dededecline/SST60/KiCad Project Files/MCU.kicad_sch

## KiCad design KiCad Project Files/MCU.kicad_sch (2022-08-14)

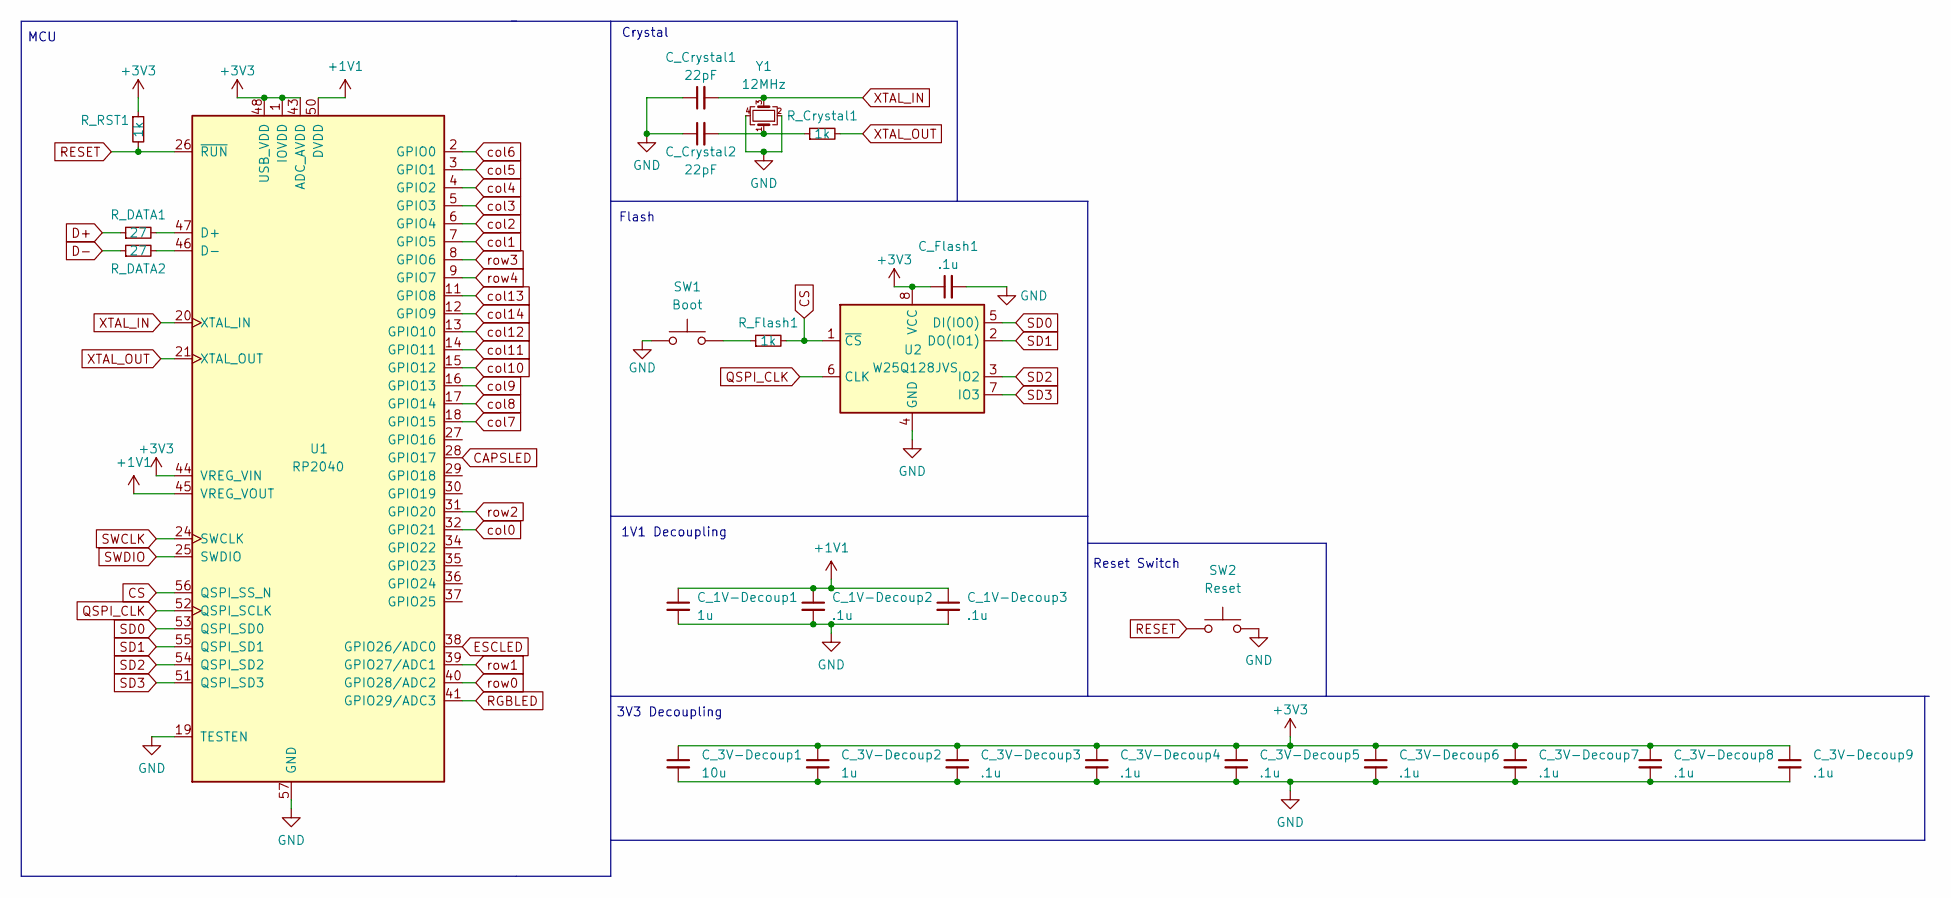
[picture p5: schematic MCU.kicad_sch]

Parts:
C_1V-Decoup1, C_3V-Decoup2: 1u; C_0402_1005Metric
C_1V-Decoup2, C_1V-Decoup3, C_3V-Decoup3, C_3V-Decoup4, C_3V-Decoup5, C_3V-Decoup6, C_3V-Decoup7, C_3V-Decoup8, C_3V-Decoup9: .1u; C_0402_1005Metric
C_3V-Decoup1: 10u; C_0402_1005Metric
C_Crystal1, C_Crystal2: 22pF; C_0402_1005Metric
C_Flash1: .1u; C_0402_1005Metric
R_Crystal1: 1k; R_0402_1005Metric
R_DATA1, R_DATA2: 27; R_0402_1005Metric
R_Flash1: 1k; R_0402_1005Metric
R_RST1: 1k; R_0402_1005Metric
SW1: Boot; SW_SPST_TL3342
SW2: Reset; SW_SPST_TL3342
U1: RP2040; RP2040-QFN-56
U2: W25Q128JVS; SOIC-8_5.23x5.23mm_P1.27mm
Y1: 12MHz; Crystal_SMD_3225-4Pin_3.2x2.5mm

Connections:
+1V1: C_1V-Decoup1.1, C_1V-Decoup2.1, C_1V-Decoup3.1, U1.23 (DVDD), U1.45 (VREG_VOUT), U1.50 (DVDD)
+3V3: C_3V-Decoup1.1, C_3V-Decoup2.1, C_3V-Decoup3.1, C_3V-Decoup4.1, C_3V-Decoup5.1, C_3V-Decoup6.1, C_3V-Decoup7.1, C_3V-Decoup8.1, C_3V-Decoup9.1, C_Flash1.1, R_RST1.1, U1.1 (IOVDD), U1.10 (IOVDD), U1.22 (IOVDD), U1.33 (IOVDD), U1.42 (IOVDD), U1.43 (ADC_AVDD), U1.44 (VREG_VIN), U1.48 (USB_VDD), U1.49 (IOVDD), U2.8 (VCC)
CAPSLED: U1.28 (GPIO17)
CS: R_Flash1.2, U1.56 (QSPI_SS_N), U2.1 (~CS)
D+: R_DATA1.1
D-: R_DATA2.1
ESCLED: U1.38 (GPIO26/ADC0)
GND: C_1V-Decoup1.2, C_1V-Decoup2.2, C_1V-Decoup3.2, C_3V-Decoup1.2, C_3V-Decoup2.2, C_3V-Decoup3.2, C_3V-Decoup4.2, C_3V-Decoup5.2, C_3V-Decoup6.2, C_3V-Decoup7.2, C_3V-Decoup8.2, C_3V-Decoup9.2, C_Crystal1.1, C_Crystal2.1, C_Flash1.2, SW1.1, SW2.2, U1.19 (TESTEN), U1.57 (GND), U2.4 (GND), Y1.2, Y1.4
unnamed: C_Crystal2.2, R_Crystal1.1, Y1.1
unnamed: R_DATA1.2, U1.47 (D+)
unnamed: R_DATA2.2, U1.46 (D-)
unnamed: R_Flash1.1, SW1.2
QSPI_CLK: U1.52 (QSPI_SCLK), U2.6 (CLK)
RESET: R_RST1.2, SW2.1, U1.26 (~RUN)
RGBLED: U1.41 (GPIO29/ADC3)
SD0: U1.53 (QSPI_SD0), U2.5 (DI(IO0))
SD1: U1.55 (QSPI_SD1), U2.2 (DO(IO1))
SD2: U1.54 (QSPI_SD2), U2.3 (IO2)
SD3: U1.51 (QSPI_SD3), U2.7 (IO3)
SWCLK: U1.24 (SWCLK)
SWDIO: U1.25 (SWDIO)
XTAL_IN: C_Crystal1.2, U1.20 (XTAL_IN), Y1.3
XTAL_OUT: R_Crystal1.2, U1.21 (XTAL_OUT)
col0: U1.32 (GPIO21)
col1: U1.7 (GPIO5)
col2: U1.6 (GPIO4)
col3: U1.5 (GPIO3)
col4: U1.4 (GPIO2)
col5: U1.3 (GPIO1)
col6: U1.2 (GPIO0)
col7: U1.18 (GPIO15)
col8: U1.17 (GPIO14)
col9: U1.16 (GPIO13)
col10: U1.15 (GPIO12)
col11: U1.14 (GPIO11)
col12: U1.13 (GPIO10)
col13: U1.11 (GPIO8)
col14: U1.12 (GPIO9)
row0: U1.40 (GPIO28/ADC2)
row1: U1.39 (GPIO27/ADC1)
row2: U1.31 (GPIO20)
row3: U1.8 (GPIO6)
row4: U1.9 (GPIO7)

Notes on the sheet:
Reset Switch
Flash
MCU
Crystal
3V3 Decoupling
1V1 Decoupling
