dededecline/SST60/KiCad Project Files/Misc.kicad_sch

## KiCad design KiCad Project Files/Misc.kicad_sch (2022-08-29)

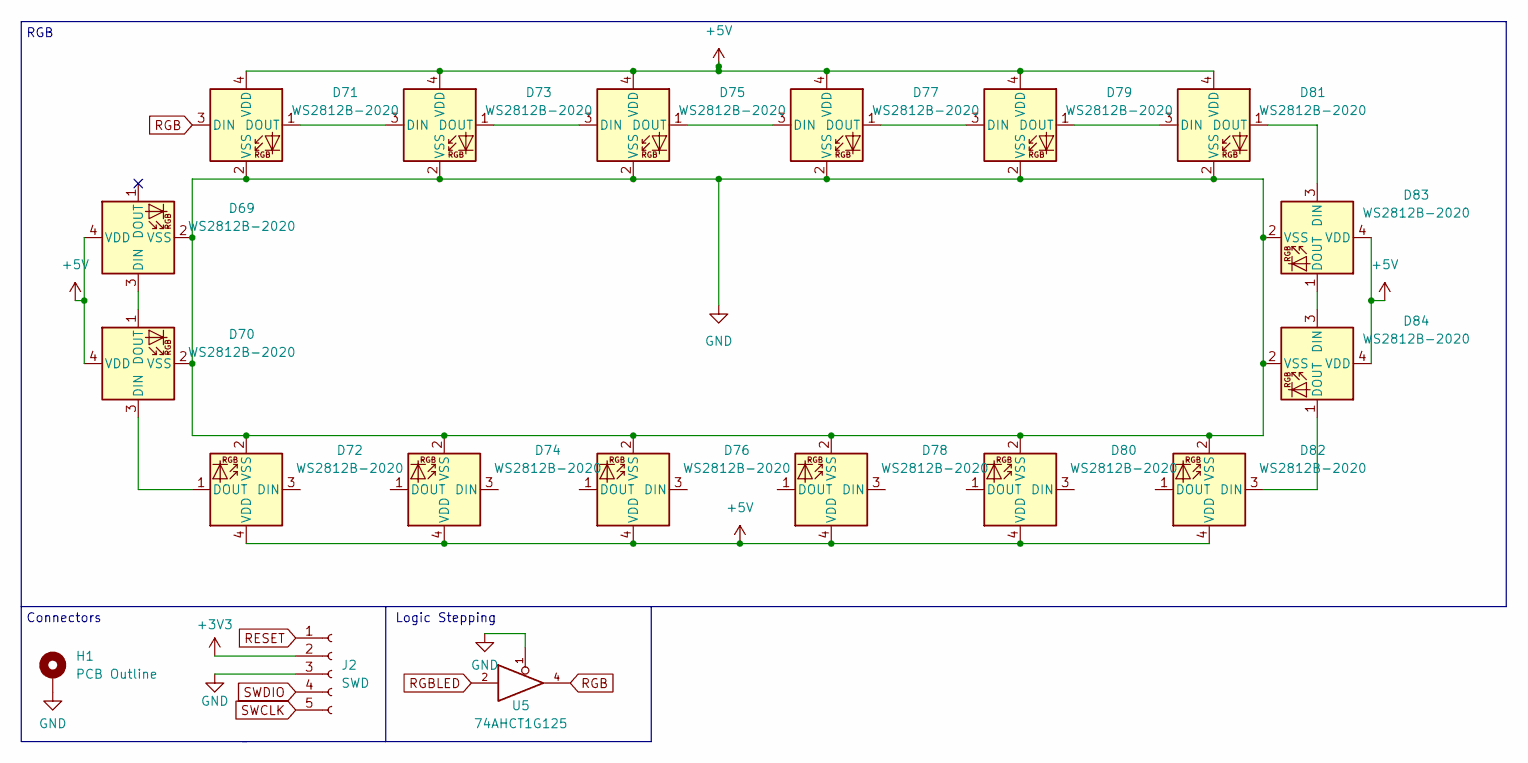
[picture p6: schematic Misc.kicad_sch]

Parts:
D69, D70, D71, D72, D73, D74, D75, D76, D77, D78, D79, D80, D81, D82, D83, D84: WS2812B-2020; LED_WS2812_2020
H1: PCB Outline; L60 Outline
J2: SWD; PinHeader_1x05_P2.54mm_Vertical
U5: 74AHCT1G125; SOT-23-5

Connections:
+3V3: J2.2
GND: D69.2 (VSS), D70.2 (VSS), D71.2 (VSS), D72.2 (VSS), D73.2 (VSS), D74.2 (VSS), D75.2 (VSS), D76.2 (VSS), D77.2 (VSS), D78.2 (VSS), D79.2 (VSS), D80.2 (VSS), D81.2 (VSS), D82.2 (VSS), D83.2 (VSS), D84.2 (VSS), H1.1, J2.3, U5.1
unnamed: D69.3 (DIN), D70.1 (DOUT)
unnamed: D69.4 (VDD), D70.4 (VDD)
unnamed: D70.3 (DIN), D72.1 (DOUT)
unnamed: D71.1 (DOUT), D73.3 (DIN)
unnamed: D71.4 (VDD), D73.4 (VDD), D75.4 (VDD), D77.4 (VDD), D79.4 (VDD), D81.4 (VDD)
unnamed: D72.4 (VDD), D74.4 (VDD), D76.4 (VDD), D78.4 (VDD), D80.4 (VDD), D82.4 (VDD)
unnamed: D73.1 (DOUT), D75.3 (DIN)
unnamed: D75.1 (DOUT), D77.3 (DIN)
unnamed: D77.1 (DOUT), D79.3 (DIN)
unnamed: D79.1 (DOUT), D81.3 (DIN)
unnamed: D81.1 (DOUT), D83.3 (DIN)
unnamed: D82.3 (DIN), D84.1 (DOUT)
unnamed: D83.1 (DOUT), D84.3 (DIN)
unnamed: D83.4 (VDD), D84.4 (VDD)
RESET: J2.1
RGB: D71.3 (DIN), U5.4
RGBLED: U5.2
SWCLK: J2.5
SWDIO: J2.4

Notes on the sheet:
Logic Stepping
Connectors
RGB
