dededecline/SST60/KiCad Project Files/Swtich Matrix.kicad_sch

## KiCad design KiCad Project Files/Swtich Matrix.kicad_sch (2022-08-14)

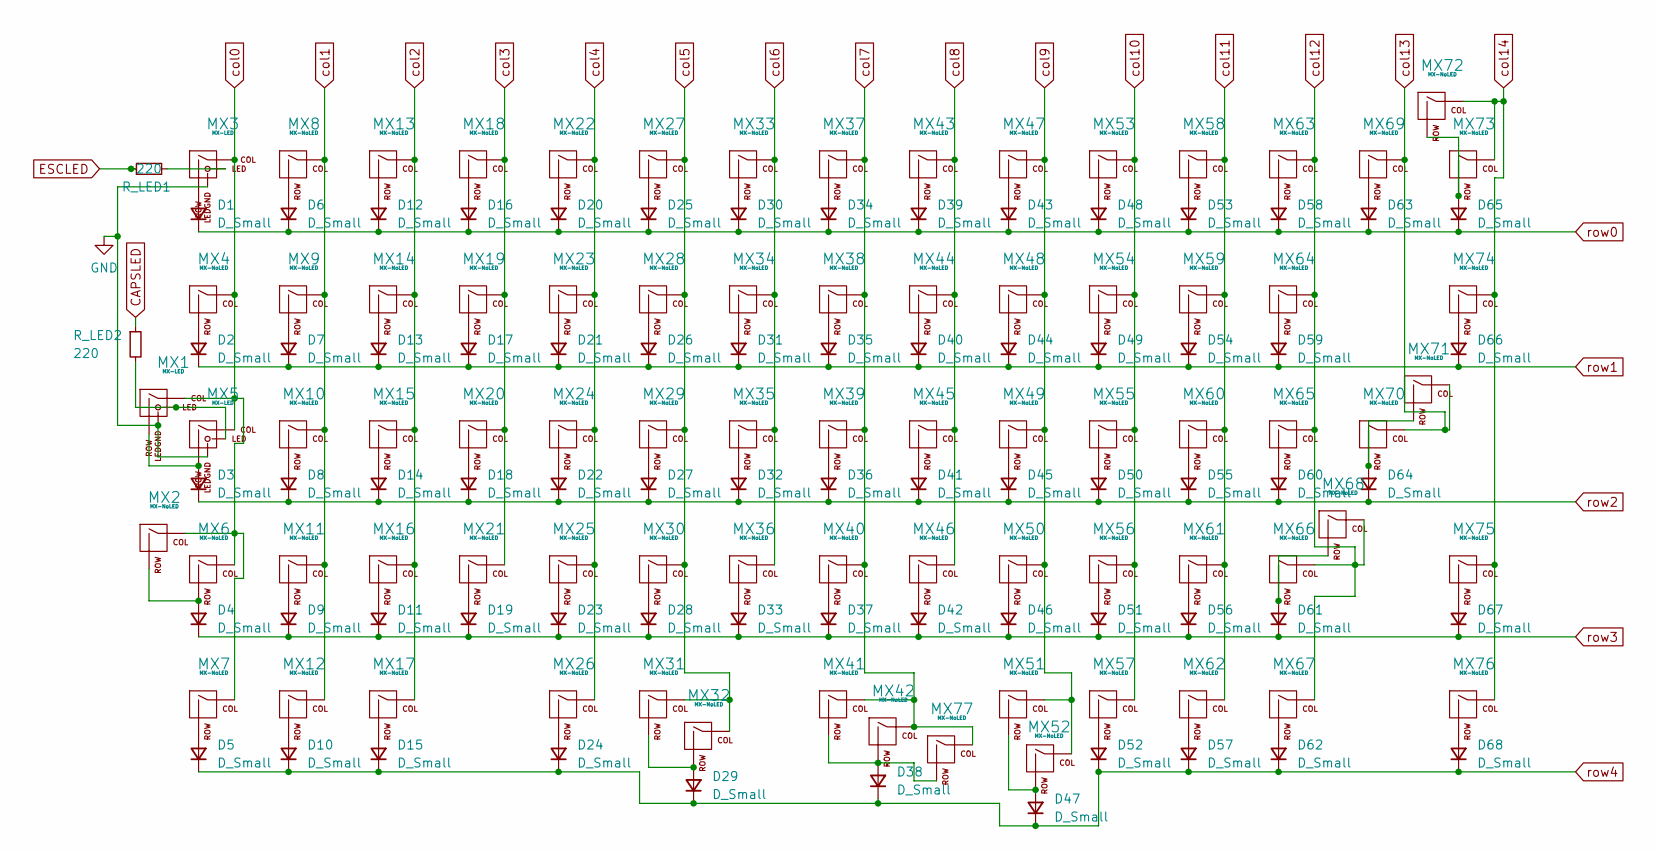
[picture p7: schematic Swtich Matrix.kicad_sch]

Parts:
D1, D2, D3, D4, D5, D6, D7, D8, D9, D10, D11, D12, D13, D14, D15, D16, D17, D18, D19, D20, D21, D22, D23, D24, D25, D26, D27, D28, D29, D30, D31, D32, D33, D34, D35, D36, D37, D38, D39, D40, D41, D42, D43, D44, D45, D46, D47, D48, D49, D50, D51, D52, D53, D54, D55, D56, D57, D58, D59, D60, D61, D62, D63, D64, D65, D66, D67, D68: D_Small; D_SOD-123
MX1: MX-LED; MX-1.25U-FLIPPED
MX2: MX-NoLED; MX-1.25U-NoLED
MX3: MX-LED; MX-1U
MX4, MX7, MX17, MX62, MX74, MX76: MX-NoLED; MX-1.5U-NoLED
MX5: MX-LED; MX-1.75U
MX6, MX70: MX-NoLED; MX-2.25U-NoLED
MX8, MX9, MX10, MX11, MX12, MX13, MX14, MX15, MX16, MX18, MX19, MX20, MX21, MX22, MX23, MX24, MX25, MX26, MX27, MX28, MX29, MX30, MX33, MX34, MX35, MX36, MX37, MX38, MX39, MX40, MX41, MX43, MX44, MX45, MX46, MX47, MX48, MX49, MX50, MX53, MX54, MX55, MX56, MX57, MX58, MX59, MX60, MX61, MX63, MX64, MX65, MX67, MX69, MX73, MX75: MX-NoLED; MX-1U-NoLED
MX31: MX-NoLED; MX-2.25U-ReversedStabilizers-NoLED
MX32, MX52: MX-NoLED; MX-3U-ReversedStabilizers-NoLED
MX42: MX-NoLED; MX-7U-ReversedStabilizers-NoLED
MX51: MX-NoLED; MX-2.75U-ReversedStabilizers-NoLED
MX66: MX-NoLED; MX-1.75U-NoLED
MX68: MX-NoLED; MX-2.75U-NoLED
MX71: MX-NoLED; MX-ISO-ReversedStabilizers
MX72: MX-NoLED; MX-2U-NoLED
MX77: MX-NoLED; MX-10U-ReversedStabilizers-NoLED
R_LED1, R_LED2: 220; R_0402_1005Metric

Connections:
CAPSLED: R_LED2.1
ESCLED: R_LED1.1
GND: MX1.4 (LEDGND), MX3.4 (LEDGND), MX5.4 (LEDGND)
unnamed: D1.2 (A), MX3.2 (ROW)
unnamed: D2.2 (A), MX4.2 (ROW)
unnamed: D3.2 (A), MX1.2 (ROW), MX5.1 (ROW)
unnamed: D4.2 (A), MX2.2 (ROW), MX6.2 (ROW)
unnamed: D5.2 (A), MX7.2 (ROW)
unnamed: D6.2 (A), MX8.2 (ROW)
unnamed: D7.2 (A), MX9.2 (ROW)
unnamed: D8.2 (A), MX10.2 (ROW)
unnamed: D9.2 (A), MX11.2 (ROW)
unnamed: D10.2 (A), MX12.2 (ROW)
unnamed: D11.2 (A), MX16.2 (ROW)
unnamed: D12.2 (A), MX13.2 (ROW)
unnamed: D13.2 (A), MX14.2 (ROW)
unnamed: D14.2 (A), MX15.2 (ROW)
unnamed: D15.2 (A), MX17.2 (ROW)
unnamed: D16.2 (A), MX18.2 (ROW)
unnamed: D17.2 (A), MX19.2 (ROW)
unnamed: D18.2 (A), MX20.2 (ROW)
unnamed: D19.2 (A), MX21.2 (ROW)
unnamed: D20.2 (A), MX22.2 (ROW)
unnamed: D21.2 (A), MX23.2 (ROW)
unnamed: D22.2 (A), MX24.2 (ROW)
unnamed: D23.2 (A), MX25.2 (ROW)
unnamed: D24.2 (A), MX26.2 (ROW)
unnamed: D25.2 (A), MX27.2 (ROW)
unnamed: D26.2 (A), MX28.2 (ROW)
unnamed: D27.2 (A), MX29.2 (ROW)
unnamed: D28.2 (A), MX30.2 (ROW)
unnamed: D29.2 (A), MX31.2 (ROW), MX32.2 (ROW)
unnamed: D30.2 (A), MX33.2 (ROW)
unnamed: D31.2 (A), MX34.2 (ROW)
unnamed: D32.2 (A), MX35.2 (ROW)
unnamed: D33.2 (A), MX36.2 (ROW)
unnamed: D34.2 (A), MX37.2 (ROW)
unnamed: D35.2 (A), MX38.2 (ROW)
unnamed: D36.2 (A), MX39.2 (ROW)
unnamed: D37.2 (A), MX40.2 (ROW)
unnamed: D38.2 (A), MX41.2 (ROW), MX42.2 (ROW), MX77.2 (ROW)
unnamed: D39.2 (A), MX43.2 (ROW)
unnamed: D40.2 (A), MX44.2 (ROW)
unnamed: D41.2 (A), MX45.2 (ROW)
unnamed: D42.2 (A), MX46.2 (ROW)
unnamed: D43.2 (A), MX47.2 (ROW)
unnamed: D44.2 (A), MX48.2 (ROW)
unnamed: D45.2 (A), MX49.2 (ROW)
unnamed: D46.2 (A), MX50.2 (ROW)
unnamed: D47.2 (A), MX51.2 (ROW), MX52.2 (ROW)
unnamed: D48.2 (A), MX53.2 (ROW)
unnamed: D49.2 (A), MX54.2 (ROW)
unnamed: D50.2 (A), MX55.2 (ROW)
unnamed: D51.2 (A), MX56.2 (ROW)
unnamed: D52.2 (A), MX57.2 (ROW)
unnamed: D53.2 (A), MX58.2 (ROW)
unnamed: D54.2 (A), MX59.2 (ROW)
unnamed: D55.2 (A), MX60.2 (ROW)
unnamed: D56.2 (A), MX61.2 (ROW)
unnamed: D57.2 (A), MX62.2 (ROW)
unnamed: D58.2 (A), MX63.2 (ROW)
unnamed: D59.2 (A), MX64.2 (ROW)
unnamed: D60.2 (A), MX65.2 (ROW)
unnamed: D61.2 (A), MX66.2 (ROW), MX68.2 (ROW)
unnamed: D62.2 (A), MX67.2 (ROW)
unnamed: D63.2 (A), MX69.2 (ROW)
unnamed: D64.2 (A), MX70.2 (ROW), MX71.2 (ROW)
unnamed: D65.2 (A), MX72.2 (ROW), MX73.2 (ROW)
unnamed: D66.2 (A), MX74.2 (ROW)
unnamed: D67.2 (A), MX75.2 (ROW)
unnamed: D68.2 (A), MX76.2 (ROW)
unnamed: MX1.3 (LED), MX5.3 (LED), R_LED2.2
unnamed: MX3.3 (LED), R_LED1.2
col0: MX1.1 (COL), MX2.1 (COL), MX3.1 (COL), MX4.1 (COL), MX5.2 (COL), MX6.1 (COL), MX7.1 (COL)
col1: MX8.1 (COL), MX9.1 (COL), MX10.1 (COL), MX11.1 (COL), MX12.1 (COL)
col2: MX13.1 (COL), MX14.1 (COL), MX15.1 (COL), MX16.1 (COL), MX17.1 (COL)
col3: MX18.1 (COL), MX19.1 (COL), MX20.1 (COL), MX21.1 (COL)
col4: MX22.1 (COL), MX23.1 (COL), MX24.1 (COL), MX25.1 (COL), MX26.1 (COL)
col5: MX27.1 (COL), MX28.1 (COL), MX29.1 (COL), MX30.1 (COL), MX31.1 (COL), MX32.1 (COL)
col6: MX33.1 (COL), MX34.1 (COL), MX35.1 (COL), MX36.1 (COL)
col7: MX37.1 (COL), MX38.1 (COL), MX39.1 (COL), MX40.1 (COL), MX41.1 (COL), MX42.1 (COL), MX77.1 (COL)
col8: MX43.1 (COL), MX44.1 (COL), MX45.1 (COL), MX46.1 (COL)
col9: MX47.1 (COL), MX48.1 (COL), MX49.1 (COL), MX50.1 (COL), MX51.1 (COL), MX52.1 (COL)
col10: MX53.1 (COL), MX54.1 (COL), MX55.1 (COL), MX56.1 (COL), MX57.1 (COL)
col11: MX58.1 (COL), MX59.1 (COL), MX60.1 (COL), MX61.1 (COL), MX62.1 (COL)
col12: MX63.1 (COL), MX64.1 (COL), MX65.1 (COL), MX66.1 (COL), MX67.1 (COL), MX68.1 (COL)
col13: MX69.1 (COL), MX70.1 (COL), MX71.1 (COL)
col14: MX72.1 (COL), MX73.1 (COL), MX74.1 (COL), MX75.1 (COL), MX76.1 (COL)
row0: D1.1 (K), D6.1 (K), D12.1 (K), D16.1 (K), D20.1 (K), D25.1 (K), D30.1 (K), D34.1 (K), D39.1 (K), D43.1 (K), D48.1 (K), D53.1 (K), D58.1 (K), D63.1 (K), D65.1 (K)
row1: D2.1 (K), D7.1 (K), D13.1 (K), D17.1 (K), D21.1 (K), D26.1 (K), D31.1 (K), D35.1 (K), D40.1 (K), D44.1 (K), D49.1 (K), D54.1 (K), D59.1 (K), D66.1 (K)
row2: D3.1 (K), D8.1 (K), D14.1 (K), D18.1 (K), D22.1 (K), D27.1 (K), D32.1 (K), D36.1 (K), D41.1 (K), D45.1 (K), D50.1 (K), D55.1 (K), D60.1 (K), D64.1 (K)
row3: D4.1 (K), D9.1 (K), D11.1 (K), D19.1 (K), D23.1 (K), D28.1 (K), D33.1 (K), D37.1 (K), D42.1 (K), D46.1 (K), D51.1 (K), D56.1 (K), D61.1 (K), D67.1 (K)
row4: D5.1 (K), D10.1 (K), D15.1 (K), D24.1 (K), D29.1 (K), D38.1 (K), D47.1 (K), D52.1 (K), D57.1 (K), D62.1 (K), D68.1 (K)
