dededecline/SST60/KiCad Project Files/USBnPower.kicad_sch

## KiCad design KiCad Project Files/USBnPower.kicad_sch (2022-07-27)

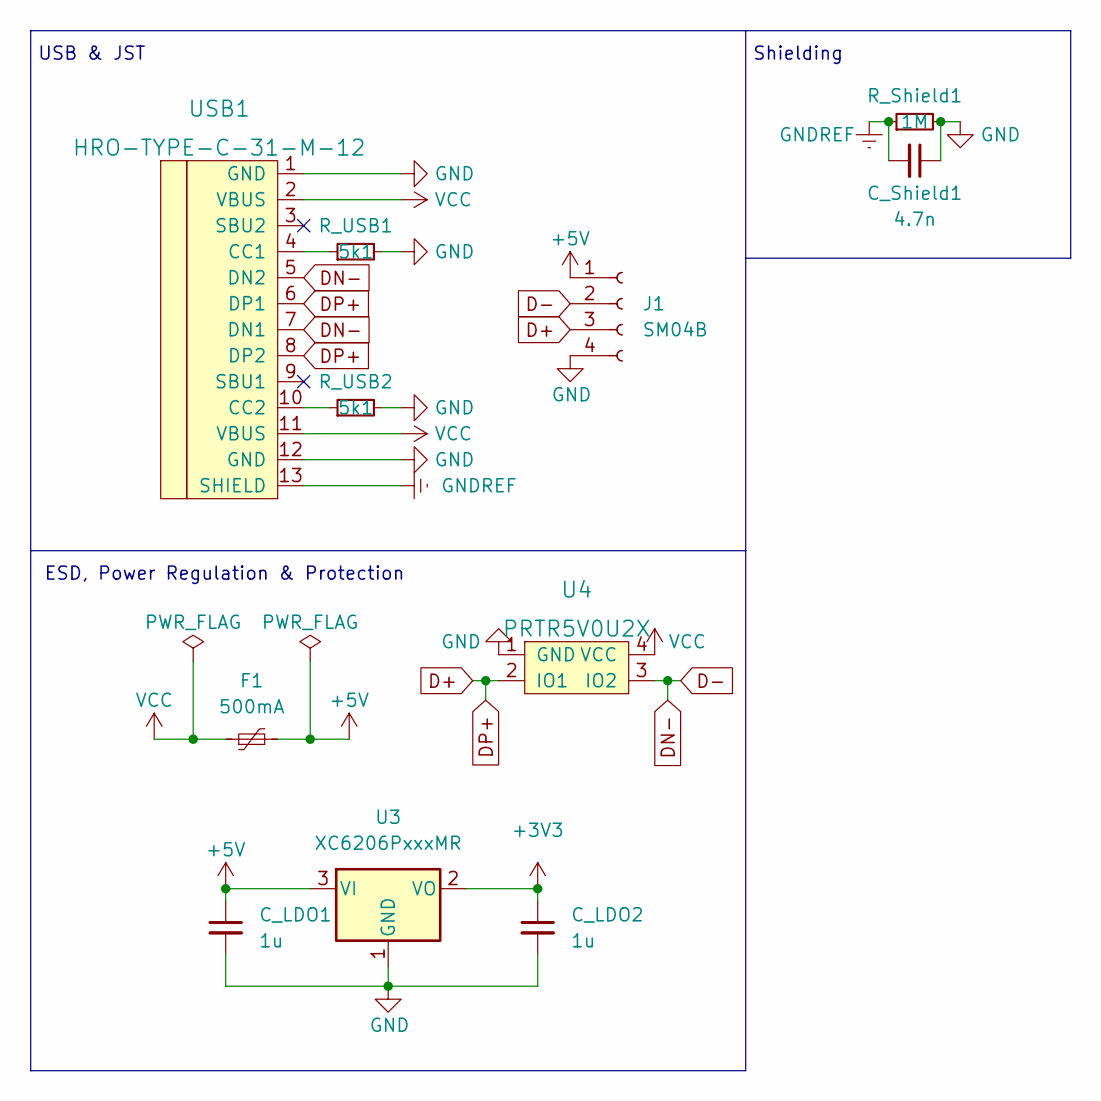
[picture p8: schematic USBnPower.kicad_sch]

Parts:
C_LDO1, C_LDO2: 1u; C_0402_1005Metric
C_Shield1: 4.7n; C_0402_1005Metric
F1: 500mA; Fuse_0805_2012Metric
J1: SM04B; JST_SH_SM04B-SRSS-TB_1x04-1MP_P1.00mm_Horizontal
R_Shield1: 1M; R_0402_1005Metric
R_USB1, R_USB2: 5k1; R_0402_1005Metric
U3: XC6206PxxxMR; SOT-23
U4: PRTR5V0U2X; SOT143B
USB1: HRO-TYPE-C-31-M-12; HRO-TYPE-C-31-M-12-Assembly

Connections:
+3V3: C_LDO2.1, U3.2 (VO)
+5V: C_LDO1.1, F1.2, J1.1, U3.3 (VI)
D+: J1.3, U4.2 (IO1), USB1.6 (DP1), USB1.8 (DP2)
D-: J1.2, U4.3 (IO2), USB1.5 (DN2), USB1.7 (DN1)
GND: C_LDO1.2, C_LDO2.2, C_Shield1.1, J1.4, R_Shield1.2, R_USB1.2, R_USB2.2, U3.1 (GND), U4.1 (GND), USB1.1 (GND), USB1.12 (GND)
GNDREF: C_Shield1.2, R_Shield1.1, USB1.13 (SHIELD)
unnamed: R_USB1.1, USB1.4 (CC1)
unnamed: R_USB2.1, USB1.10 (CC2)
VCC: F1.1, U4.4 (VCC), USB1.2 (VBUS), USB1.11 (VBUS)

Notes on the sheet:
Shielding
ESD, Power Regulation & Protection
USB & JST
