dededecline/SST60/Hotswap/KiCad/SST60HS.kicad_sch

## KiCad design Hotswap/KiCad/SST60HS.kicad_sch (2023-03-09)

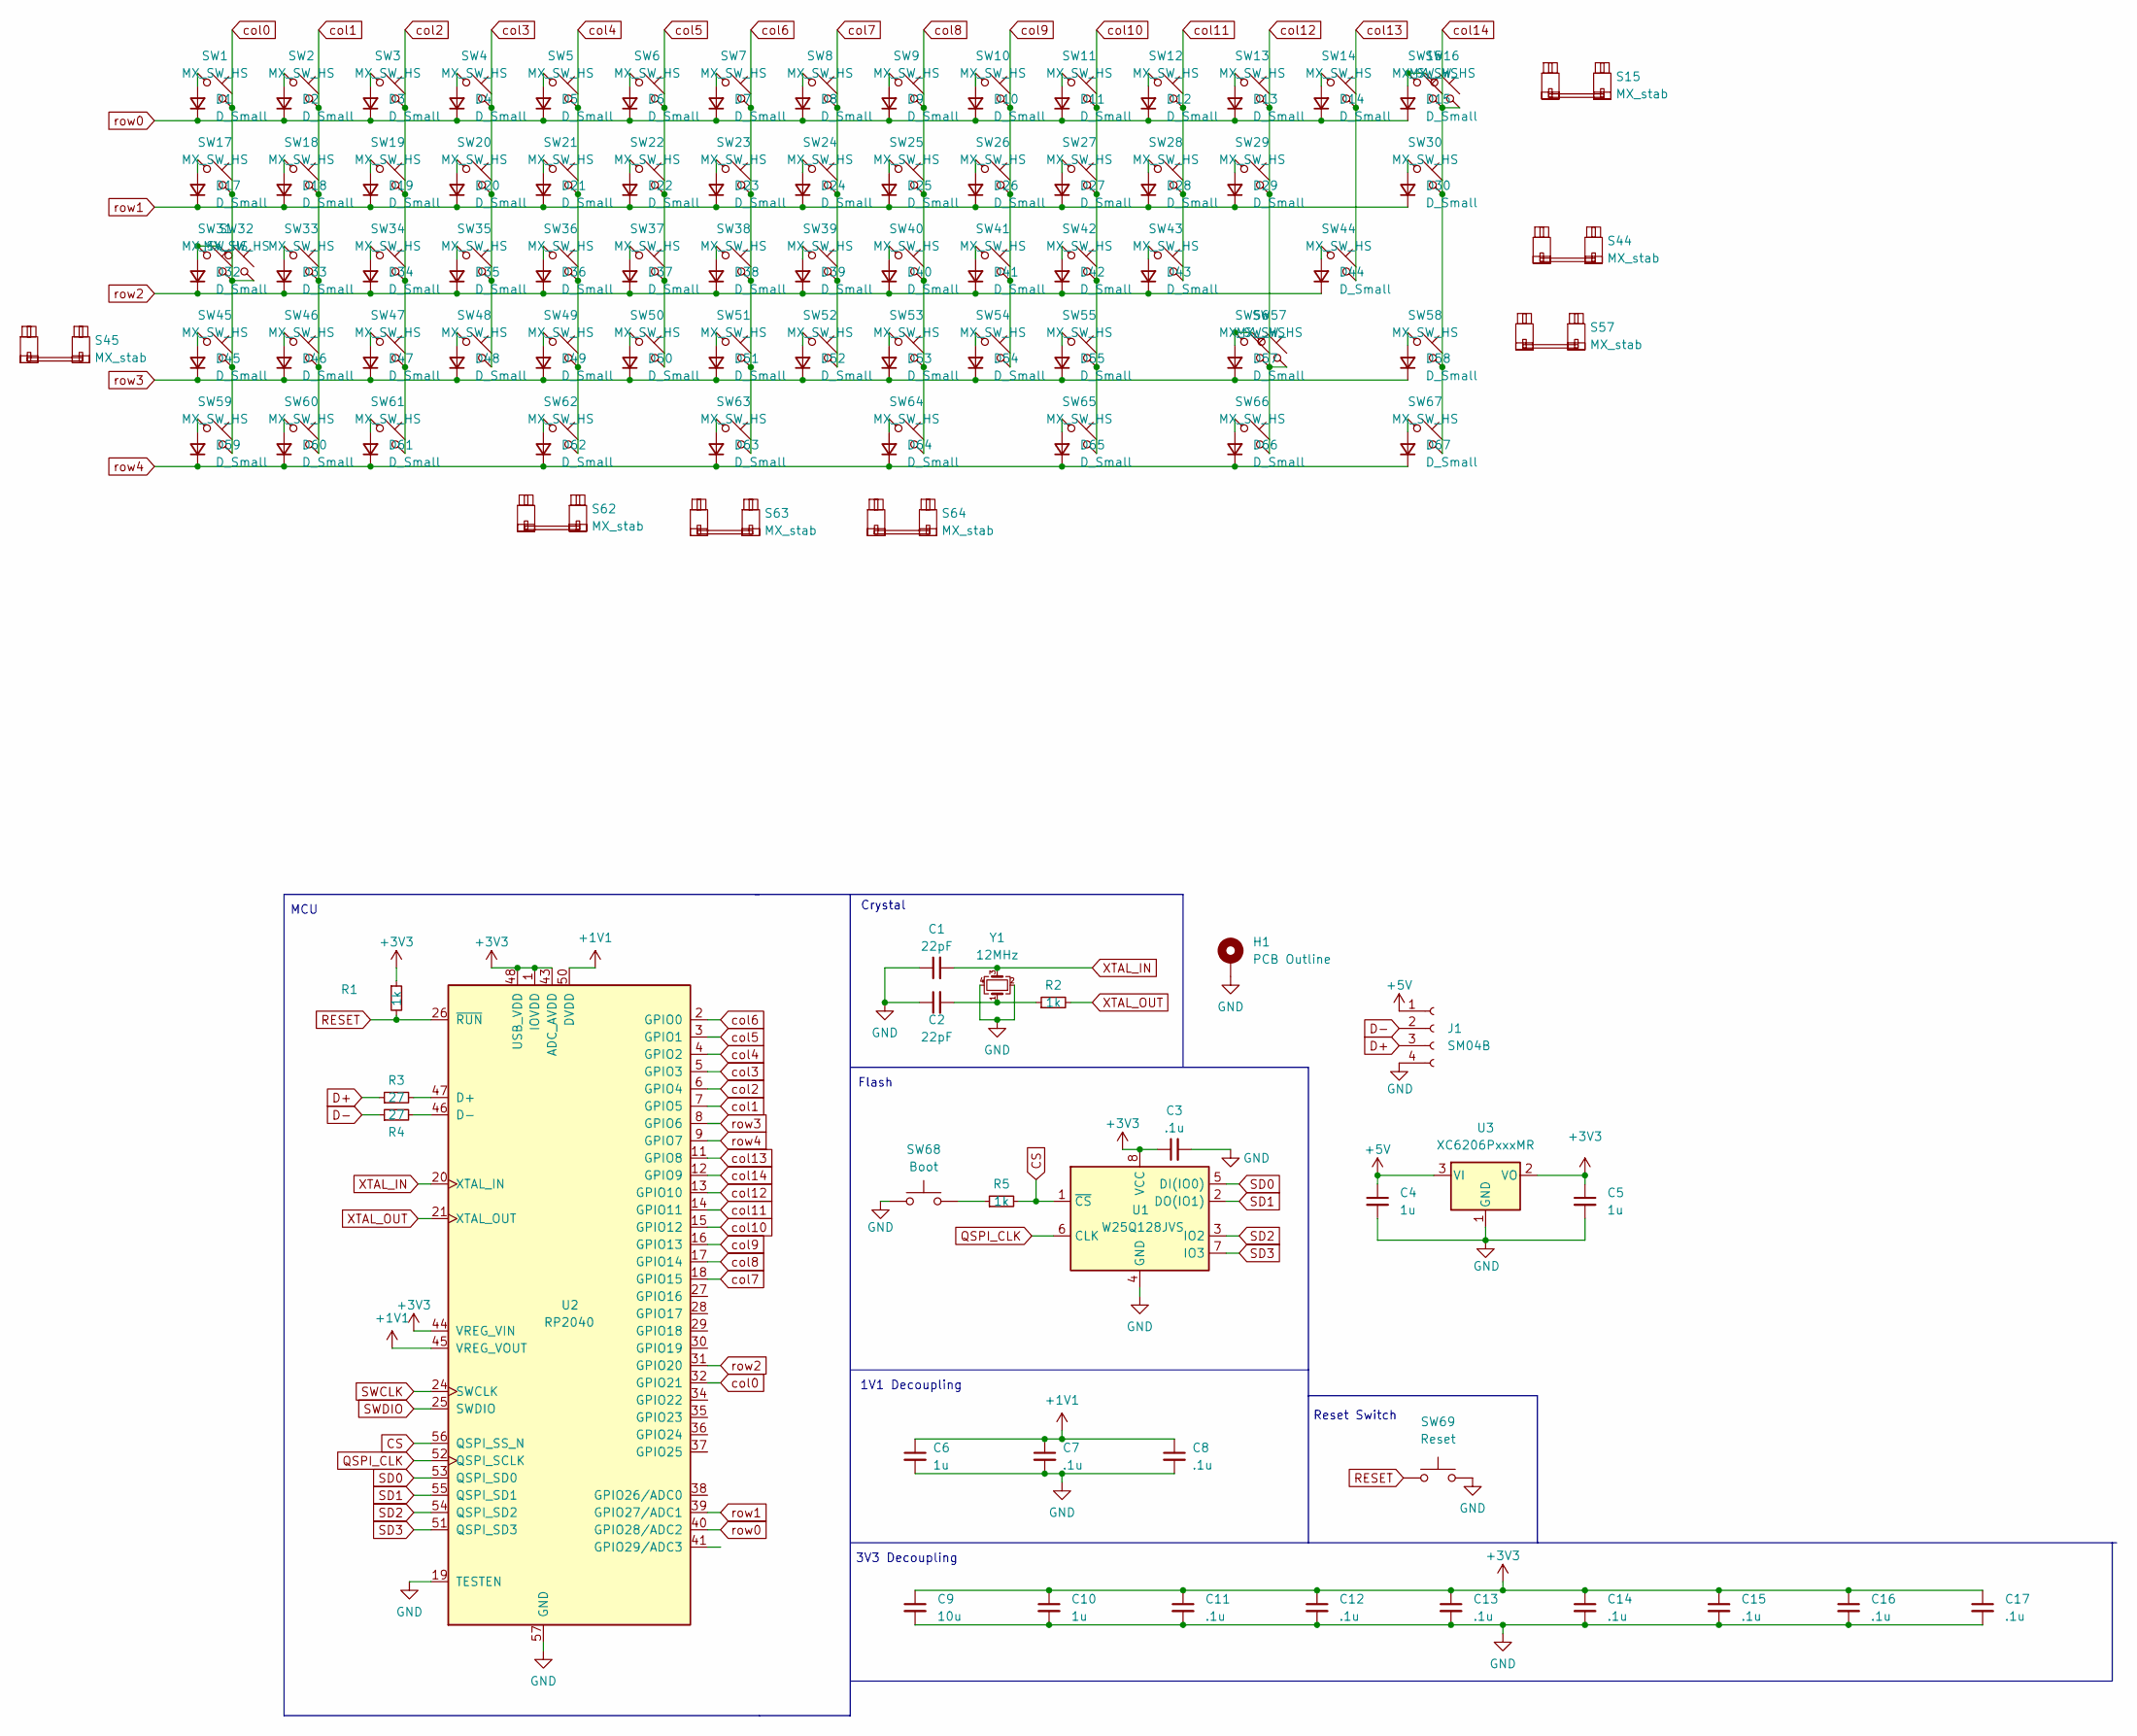
[picture p9: schematic SST60HS.kicad_sch]

Parts:
C1, C2: 22pF; C_0402_1005Metric
C3, C7, C8, C11, C12, C13, C14, C15, C16, C17: .1u; C_0402_1005Metric
C4, C5, C6, C10: 1u; C_0402_1005Metric
C9: 10u; C_0402_1005Metric
D1, D2, D3, D4, D5, D6, D7, D8, D9, D10, D11, D12, D13, D14, D15, D17, D18, D19, D20, D21, D22, D23, D24, D25, D26, D27, D28, D29, D30, D32, D33, D34, D35, D36, D37, D38, D39, D40, D41, D42, D43, D44, D45, D46, D47, D48, D49, D50, D51, D52, D53, D54, D55, D57, D58, D59, D60, D61, D62, D63, D64, D65, D66, D67: D_Small; D_SOD-123
H1: PCB Outline; L60 Outline
J1: SM04B; Molex_Pico-EZmate_78171-0004_1x04-1MP_P1.20mm_Vertical
R1, R2, R5: 1k; R_0402_1005Metric
R3, R4: 27; R_0402_1005Metric
S15: MX_stab; STAB_MX_P_2u
S44, S45: MX_stab; STAB_MX_P_2.25u
S57: MX_stab; STAB_MX_P_2.75u
S62, S64: MX_stab; STAB_MX_P_3u
S63: MX_stab; STAB_MX_P_7u
SW1, SW2, SW3, SW4, SW5, SW6, SW7, SW8, SW9, SW10, SW11, SW12, SW13, SW14, SW15, SW16, SW17, SW18, SW19, SW20, SW21, SW22, SW23, SW24, SW25, SW26, SW27, SW28, SW29, SW30, SW31, SW32, SW33, SW34, SW35, SW36, SW37, SW38, SW39, SW40, SW41, SW42, SW43, SW44, SW45, SW46, SW47, SW48, SW49, SW50, SW51, SW52, SW53, SW54, SW55, SW56, SW57, SW58, SW59, SW60, SW61, SW62, SW63, SW64, SW65, SW66, SW67: MX_SW_HS; SW_MX_HS_1u
SW68: Boot; SW_SPST_TL3342
SW69: Reset; SW_SPST_TL3342
U1: W25Q128JVS; SOIC-8_5.23x5.23mm_P1.27mm
U2: RP2040; RP2040-QFN-56
U3: XC6206PxxxMR; SOT-23
Y1: 12MHz; Crystal_SMD_3225-4Pin_3.2x2.5mm

Connections:
+1V1: C6.1, C7.1, C8.1, U2.23 (DVDD), U2.45 (VREG_VOUT), U2.50 (DVDD)
+3V3: C3.1, C5.1, C9.1, C10.1, C11.1, C12.1, C13.1, C14.1, C15.1, C16.1, C17.1, R1.1, U1.8 (VCC), U2.1 (IOVDD), U2.10 (IOVDD), U2.22 (IOVDD), U2.33 (IOVDD), U2.42 (IOVDD), U2.43 (ADC_AVDD), U2.44 (VREG_VIN), U2.48 (USB_VDD), U2.49 (IOVDD), U3.2 (VO)
+5V: C4.1, J1.1, U3.3 (VI)
CS: R5.2, U1.1 (~CS), U2.56 (QSPI_SS_N)
D+: J1.3, R3.1
D-: J1.2, R4.1
GND: C1.1, C2.1, C3.2, C4.2, C5.2, C6.2, C7.2, C8.2, C9.2, C10.2, C11.2, C12.2, C13.2, C14.2, C15.2, C16.2, C17.2, H1.1, J1.4, SW68.1, SW69.2, U1.4 (GND), U2.19 (TESTEN), U2.57 (GND), U3.1 (GND), Y1.2, Y1.4
unnamed: C2.2, R2.1, Y1.1
unnamed: D1.2 (A), SW1.1
unnamed: D2.2 (A), SW2.1
unnamed: D3.2 (A), SW3.1
unnamed: D4.2 (A), SW4.1
unnamed: D5.2 (A), SW5.1
unnamed: D6.2 (A), SW6.1
unnamed: D7.2 (A), SW7.1
unnamed: D8.2 (A), SW8.1
unnamed: D9.2 (A), SW9.1
unnamed: D10.2 (A), SW10.1
unnamed: D11.2 (A), SW11.1
unnamed: D12.2 (A), SW12.1
unnamed: D13.2 (A), SW13.1
unnamed: D14.2 (A), SW14.1
unnamed: D15.2 (A), SW15.1, SW16.1
unnamed: D17.2 (A), SW17.1
unnamed: D18.2 (A), SW18.1
unnamed: D19.2 (A), SW19.1
unnamed: D20.2 (A), SW20.1
unnamed: D21.2 (A), SW21.1
unnamed: D22.2 (A), SW22.1
unnamed: D23.2 (A), SW23.1
unnamed: D24.2 (A), SW24.1
unnamed: D25.2 (A), SW25.1
unnamed: D26.2 (A), SW26.1
unnamed: D27.2 (A), SW27.1
unnamed: D28.2 (A), SW28.1
unnamed: D29.2 (A), SW29.1
unnamed: D30.2 (A), SW30.1
unnamed: D32.2 (A), SW31.1, SW32.1
unnamed: D33.2 (A), SW33.1
unnamed: D34.2 (A), SW34.1
unnamed: D35.2 (A), SW35.1
unnamed: D36.2 (A), SW36.1
unnamed: D37.2 (A), SW37.1
unnamed: D38.2 (A), SW38.1
unnamed: D39.2 (A), SW39.1
unnamed: D40.2 (A), SW40.1
unnamed: D41.2 (A), SW41.1
unnamed: D42.2 (A), SW42.1
unnamed: D43.2 (A), SW43.1
unnamed: D44.2 (A), SW44.1
unnamed: D45.2 (A), SW45.1
unnamed: D46.2 (A), SW46.1
unnamed: D47.2 (A), SW47.1
unnamed: D48.2 (A), SW48.1
unnamed: D49.2 (A), SW49.1
unnamed: D50.2 (A), SW50.1
unnamed: D51.2 (A), SW51.1
unnamed: D52.2 (A), SW52.1
unnamed: D53.2 (A), SW53.1
unnamed: D54.2 (A), SW54.1
unnamed: D55.2 (A), SW55.1
unnamed: D57.2 (A), SW56.1, SW57.1
unnamed: D58.2 (A), SW58.1
unnamed: D59.2 (A), SW59.1
unnamed: D60.2 (A), SW60.1
unnamed: D61.2 (A), SW61.1
unnamed: D62.2 (A), SW62.1
unnamed: D63.2 (A), SW63.1
unnamed: D64.2 (A), SW64.1
unnamed: D65.2 (A), SW65.1
unnamed: D66.2 (A), SW66.1
unnamed: D67.2 (A), SW67.1
unnamed: R3.2, U2.47 (D+)
unnamed: R4.2, U2.46 (D-)
unnamed: R5.1, SW68.2
QSPI_CLK: U1.6 (CLK), U2.52 (QSPI_SCLK)
RESET: R1.2, SW69.1, U2.26 (~RUN)
SD0: U1.5 (DI(IO0)), U2.53 (QSPI_SD0)
SD1: U1.2 (DO(IO1)), U2.55 (QSPI_SD1)
SD2: U1.3 (IO2), U2.54 (QSPI_SD2)
SD3: U1.7 (IO3), U2.51 (QSPI_SD3)
SWCLK: U2.24 (SWCLK)
SWDIO: U2.25 (SWDIO)
XTAL_IN: C1.2, U2.20 (XTAL_IN), Y1.3
XTAL_OUT: R2.2, U2.21 (XTAL_OUT)
col0: SW1.2, SW17.2, SW31.2, SW32.2, SW45.2, SW59.2, U2.32 (GPIO21)
col1: SW2.2, SW18.2, SW33.2, SW46.2, SW60.2, U2.7 (GPIO5)
col2: SW3.2, SW19.2, SW34.2, SW47.2, SW61.2, U2.6 (GPIO4)
col3: SW4.2, SW20.2, SW35.2, SW48.2, U2.5 (GPIO3)
col4: SW5.2, SW21.2, SW36.2, SW49.2, SW62.2, U2.4 (GPIO2)
col5: SW6.2, SW22.2, SW37.2, SW50.2, U2.3 (GPIO1)
col6: SW7.2, SW23.2, SW38.2, SW51.2, SW63.2, U2.2 (GPIO0)
col7: SW8.2, SW24.2, SW39.2, SW52.2, U2.18 (GPIO15)
col8: SW9.2, SW25.2, SW40.2, SW53.2, SW64.2, U2.17 (GPIO14)
col9: SW10.2, SW26.2, SW41.2, SW54.2, U2.16 (GPIO13)
col10: SW11.2, SW27.2, SW42.2, SW55.2, SW65.2, U2.15 (GPIO12)
col11: SW12.2, SW28.2, SW43.2, U2.14 (GPIO11)
col12: SW13.2, SW29.2, SW56.2, SW57.2, SW66.2, U2.13 (GPIO10)
col13: SW14.2, SW44.2, U2.11 (GPIO8)
col14: SW15.2, SW16.2, SW30.2, SW58.2, SW67.2, U2.12 (GPIO9)
row0: D1.1 (K), D2.1 (K), D3.1 (K), D4.1 (K), D5.1 (K), D6.1 (K), D7.1 (K), D8.1 (K), D9.1 (K), D10.1 (K), D11.1 (K), D12.1 (K), D13.1 (K), D14.1 (K), D15.1 (K), U2.40 (GPIO28/ADC2)
row1: D17.1 (K), D18.1 (K), D19.1 (K), D20.1 (K), D21.1 (K), D22.1 (K), D23.1 (K), D24.1 (K), D25.1 (K), D26.1 (K), D27.1 (K), D28.1 (K), D29.1 (K), D30.1 (K), U2.39 (GPIO27/ADC1)
row2: D32.1 (K), D33.1 (K), D34.1 (K), D35.1 (K), D36.1 (K), D37.1 (K), D38.1 (K), D39.1 (K), D40.1 (K), D41.1 (K), D42.1 (K), D43.1 (K), D44.1 (K), U2.31 (GPIO20)
row3: D45.1 (K), D46.1 (K), D47.1 (K), D48.1 (K), D49.1 (K), D50.1 (K), D51.1 (K), D52.1 (K), D53.1 (K), D54.1 (K), D55.1 (K), D57.1 (K), D58.1 (K), U2.8 (GPIO6)
row4: D59.1 (K), D60.1 (K), D61.1 (K), D62.1 (K), D63.1 (K), D64.1 (K), D65.1 (K), D66.1 (K), D67.1 (K), U2.9 (GPIO7)

Notes on the sheet:
Crystal
MCU
Flash
3V3 Decoupling
1V1 Decoupling
Reset Switch
